vbalsan/rpi_pico_fakefire/values.h

#include <stdlib.h>

unsigned char yellow_array_dec[256u] = {194, 124, 128, 105, 251, 13, 29, 46, 49, 195, 95, 64, 182, 194, 20, 97, 
20, 169, 41, 72, 122, 108, 123, 142, 95, 183, 72, 168, 230, 5, 157, 7, 48, 141, 19, 122, 130, 109, 159, 139, 54, 
35, 172, 2, 102, 208, 192, 208, 121, 139, 3, 160, 13, 35, 62, 18, 198, 127, 222, 219, 86, 121, 18, 234, 82, 86, 
52, 110, 211, 50, 240, 98, 221, 125, 29, 73, 21, 78, 128, 29, 69, 43, 91, 125, 227, 96, 15, 87, 153, 240, 141, 
248, 245, 227, 190, 214, 17, 111, 99, 20, 80, 73, 196, 23, 245, 140, 244, 67, 241, 221, 159, 41, 127, 69, 59, 
218, 186, 175, 66, 101, 91, 82, 132, 8, 252, 95, 187, 19, 237, 207, 201, 240, 110, 239, 80, 71, 37, 30, 194, 46, 
154, 37, 34, 182, 32, 120, 180, 52, 190, 251, 227, 52, 90, 197, 129, 143, 214, 89, 155, 125, 117, 170, 31, 44, 
154, 150, 149, 36, 61, 171, 248, 3, 136, 39, 111, 246, 26, 217, 30, 14, 113, 182, 125, 72, 16, 212, 231, 214, 
35, 18, 67, 18, 5, 187, 113, 67, 224, 146, 218, 199, 76, 120, 151, 56, 193, 205, 236, 106, 203, 172, 155, 213, 
122, 93, 188, 112, 179, 31, 197, 233, 163, 137, 105, 135, 210, 133, 86, 175, 231, 30, 38, 19, 206, 112, 129, 126, 
149, 196, 174, 231, 193, 84, 160, 240, 194, 76, 88, 154, 66, 49, 131, 75, 40, 254, 156, 86}; 


unsigned char red_arr[256u] = {179, 164, 182, 246, 232, 157, 188, 164, 118, 134, 142, 113, 208, 203, 220, 103,
 194, 123, 223, 201, 190, 241, 217, 125, 149, 221, 233, 220, 208, 254, 199, 198, 133, 111, 203, 110, 116, 178,
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
        24, 22, 22, 24, 23, 24, 21, 25, 20, 23, 21, 20, 25, 24, 23, 23, 20, 22, 22, 23, 23, 20, 23, 20, 24, 25, 21,
         24, 24, 24, 20, 21, 23, 21, 21, 24, 24, 24, 25, 24, 22, 23, 24, 22, 24, 24, 20, 21};

unsigned char blu_arr[256u] = {2, 3, 4, 4, 1, 0, 4, 4, 1, 4, 0, 1, 5, 0, 0, 0, 3, 4, 4, 0, 2, 5, 3, 4, 5, 1, 4, 5, 0, 4,
 0, 3, 2, 1, 4, 4, 2, 0, 5, 0, 1, 4, 1, 3, 2, 3, 2, 1, 5, 0, 5, 5, 3, 3, 4, 5, 2, 5, 2, 5, 0, 0, 1, 3, 3, 2, 1, 1, 1, 3,
  4, 4, 3, 4, 1, 0, 0, 0, 4, 0, 1, 0, 5, 0, 4, 3, 2, 5, 1, 0, 1, 1, 0, 2, 1, 1, 5, 2, 1, 1, 2, 1, 0, 4, 5, 0, 0, 3, 4, 0,
   3, 0, 0, 3, 4, 3, 3, 5, 4, 3, 0, 4, 2, 2, 0, 2, 0, 5, 0, 2, 1, 2, 0, 4, 3, 1, 0, 4, 0, 4, 2, 1, 3, 2, 5, 0, 4, 0, 2, 5,
    5, 1, 5, 0, 2, 1, 3, 4, 1, 0, 2, 3, 3, 5, 2, 3, 4, 1, 5, 5, 5, 5, 5, 0, 0, 4, 3, 5, 5, 3, 0, 1, 1, 3, 2, 2, 4, 2, 5,
     0, 2, 1, 5, 1, 1, 4, 0, 5, 1, 3, 1, 0, 2, 3, 5, 5, 5, 4, 2, 5, 5, 0, 3, 4, 0, 5, 4, 4, 5, 2, 0, 1, 1, 2, 0, 2, 4, 0,
      5, 4, 4, 0, 5, 3, 2, 5, 0, 2, 5, 2, 3, 1, 0, 0, 1, 0, 3, 2, 0, 3, 2, 0, 1, 3, 0, 1};
